rabs664/Amstrad-CPC-Z80-DART/Images/DRTTST01-Putty-Session.JPG

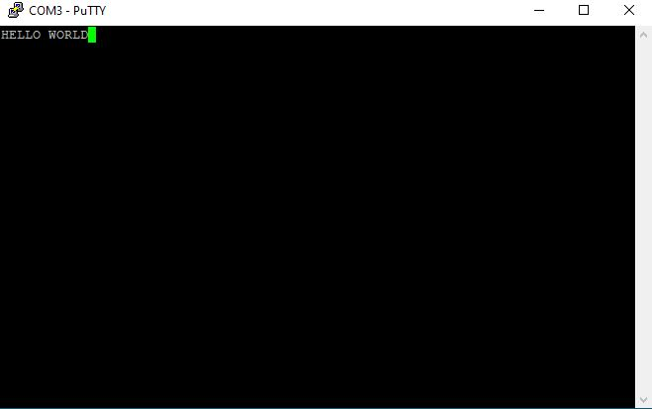
Images/DRTTST01-Putty-Session.JPG
